colemanjw2/diy-oscilloscope/Project Reference Webpage Complete/DIY CRT Oscilliscope Page_files/circ215.gif

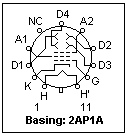
Project Reference Webpage Complete/DIY CRT Oscilliscope Page_files/circ215.gif
